zhangbokang/PCB_Fixture/五金标准件/M3×6平头或沉头螺丝.SLDPRT

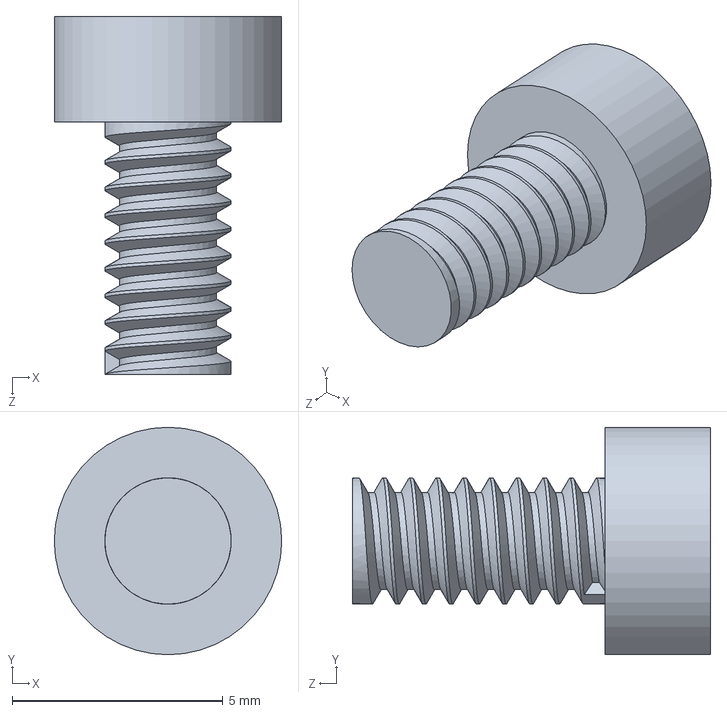
[picture p43: CAD file, 2024-11-04]
五金标准件/M3×6平头或沉头螺丝.SLDPRT
5.40 x 5.40 x 8.50 mm
