zhangbokang/PCB_Fixture/CNC加工件/夹具CNC夹片/1.4/step加工文件/CNC加工件-v1.4.1_嘉立创-固定-20250729.STEP

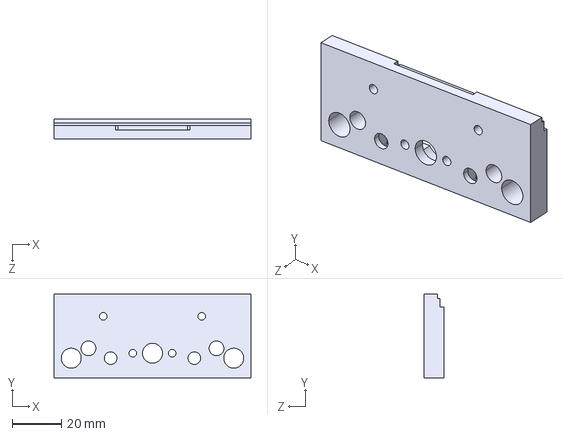
[picture p44: CAD file, 2025-07-29]
CNC加工件/夹具CNC夹片/1.4/step加工文件/CNC加工件-v1.4.1_嘉立创-固定-20250729.STEP
80.0 x 34.0 x 8.00 mm
