zhangbokang/PCB_Fixture/五金标准件/M3×20杯头螺丝.SLDPRT

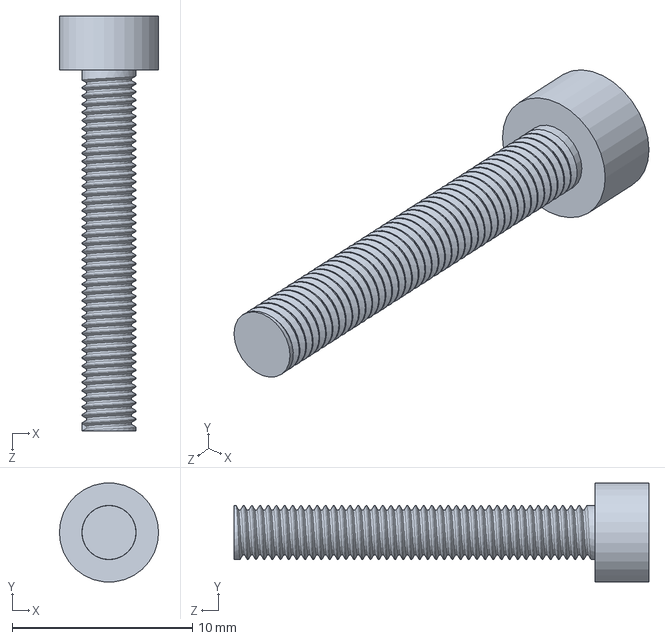
[picture p45: CAD file, 2024-11-01]
五金标准件/M3×20杯头螺丝.SLDPRT
5.50 x 5.47 x 23.0 mm
