zhangbokang/PCB_Fixture/五金标准件/T8螺杆.SLDPRT

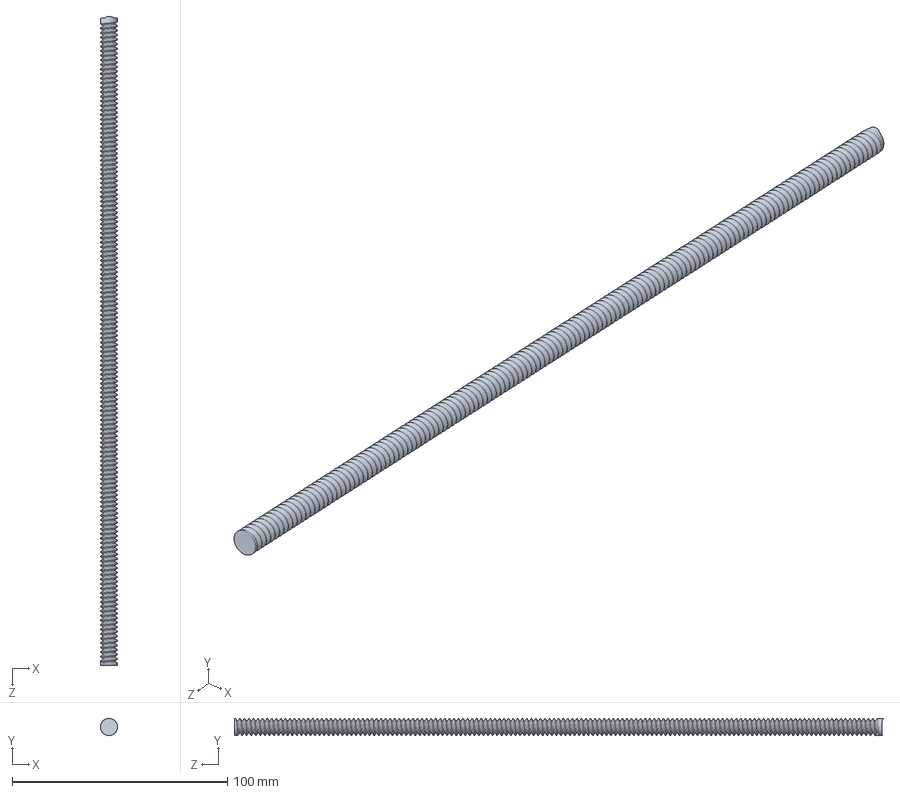
[picture p46: CAD file, 2024-11-01]
五金标准件/T8螺杆.SLDPRT
8.00 x 8.00 x 301.7 mm
