zhangbokang/PCB_Fixture/五金标准件/M5六角螺母.SLDPRT

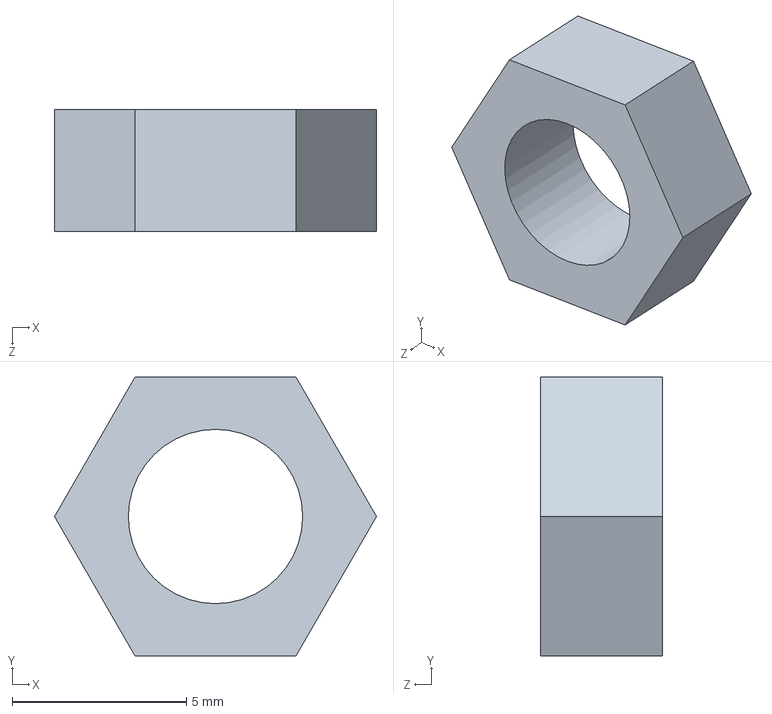
[picture p47: CAD file, 2024-11-01]
五金标准件/M5六角螺母.SLDPRT
9.24 x 8.00 x 3.50 mm
