zhangbokang/PCB_Fixture/五金标准件/M5×12杯头螺丝.SLDPRT

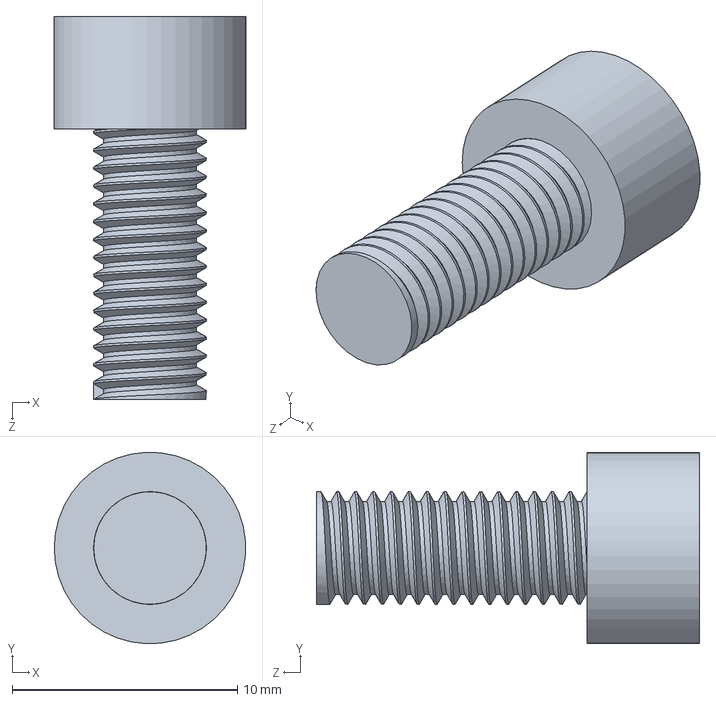
[picture p48: CAD file, 2024-11-01]
五金标准件/M5×12杯头螺丝.SLDPRT
8.50 x 8.49 x 17.0 mm
