zhangbokang/PCB_Fixture/CNC加工件/夹具CNC夹片/1.4/step加工文件/CNC加工件-v1.4.0_嘉立创-活动-20250407.STEP

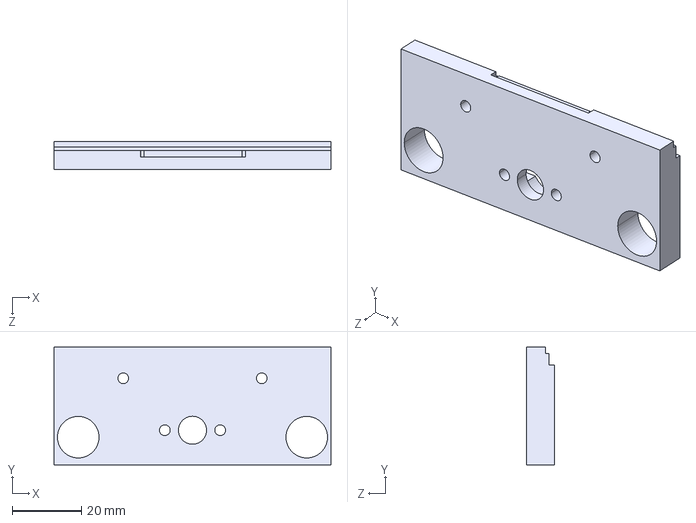
[picture p49: CAD file, 2025-07-19]
CNC加工件/夹具CNC夹片/1.4/step加工文件/CNC加工件-v1.4.0_嘉立创-活动-20250407.STEP
80.0 x 34.0 x 8.00 mm
