zhangbokang/PCB_Fixture/五金标准件/T8切边法兰.SLDPRT

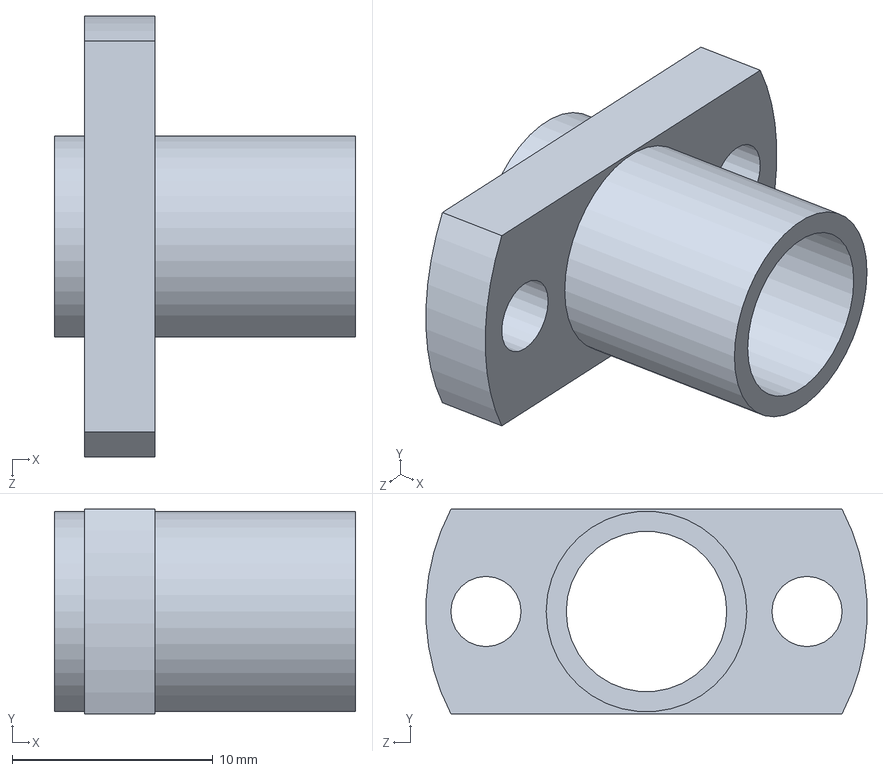
[picture p50: CAD file, 2024-11-01]
五金标准件/T8切边法兰.SLDPRT
15.0 x 10.2 x 22.0 mm
