zhangbokang/PCB_Fixture/五金标准件/铝合金手轮圆形旋钮.SLDPRT

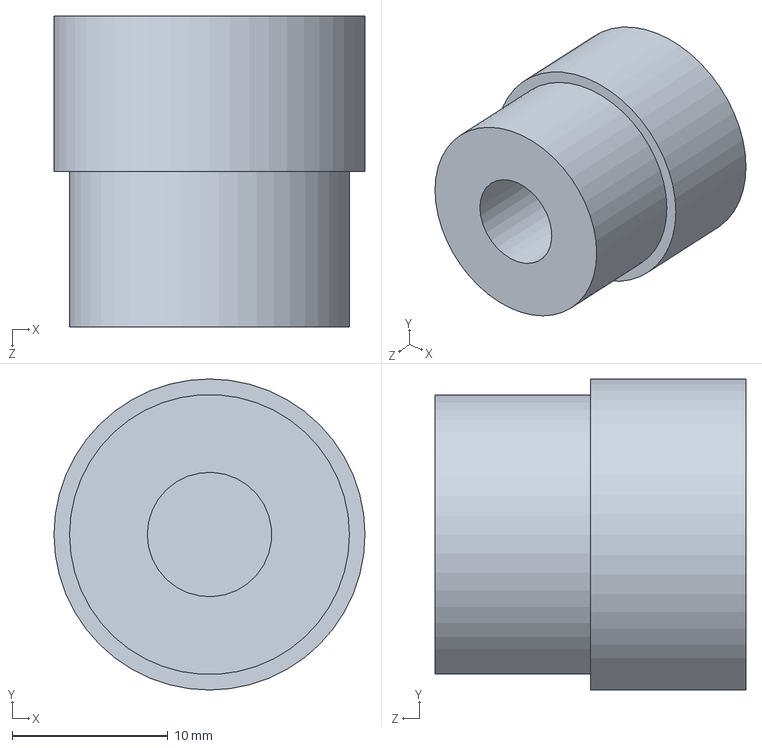
[picture p51: CAD file, 2024-11-01]
五金标准件/铝合金手轮圆形旋钮.SLDPRT
20.0 x 20.0 x 20.0 mm
