zhangbokang/PCB_Fixture/五金标准件/M3六角螺母.SLDPRT

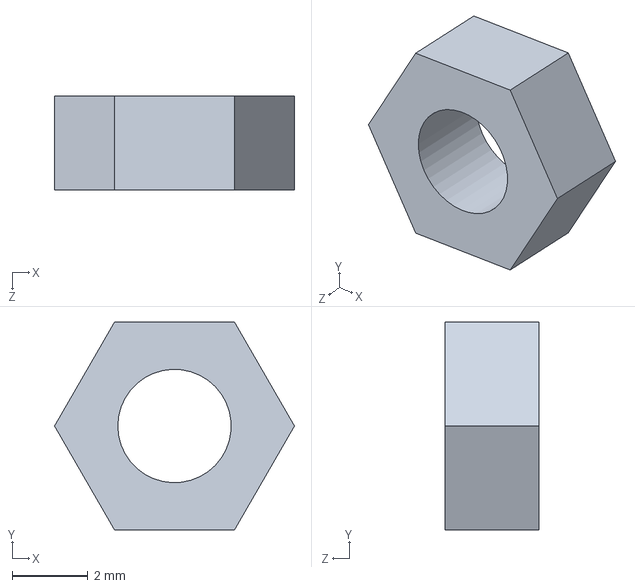
[picture p52: CAD file, 2024-11-01]
五金标准件/M3六角螺母.SLDPRT
6.35 x 5.50 x 2.50 mm
