zhangbokang/PCB_Fixture/五金标准件/SHF8-卧式支架光轴支架.SLDPRT

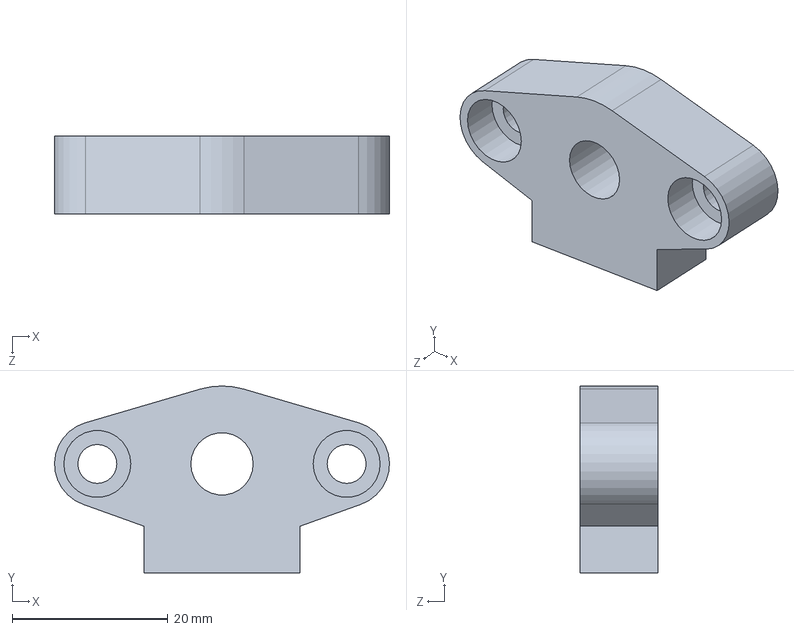
[picture p53: CAD file, 2024-11-01]
五金标准件/SHF8-卧式支架光轴支架.SLDPRT
43.0 x 24.0 x 10.0 mm
