zhangbokang/PCB_Fixture/五金标准件/光轴8mm.SLDPRT

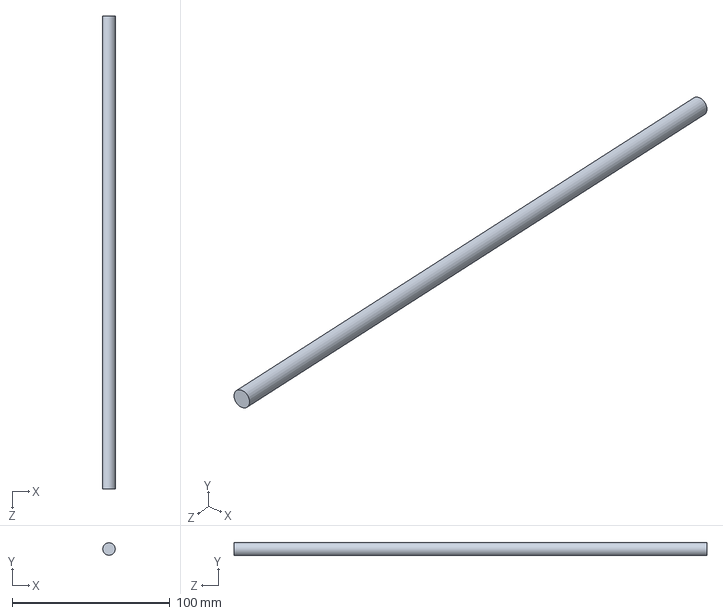
[picture p54: CAD file, 2024-11-01]
五金标准件/光轴8mm.SLDPRT
8.00 x 8.00 x 300.0 mm
